pipozoft/astrobot/eyes/heart_eye/astrobot11.png

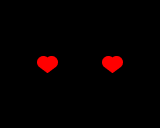
eyes/heart_eye/astrobot11.png
