pipozoft/astrobot/eyes/heart_eye/astrobot18.png

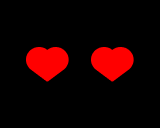
eyes/heart_eye/astrobot18.png
