pipozoft/astrobot/eyes/heart_eye/astrobot23.png

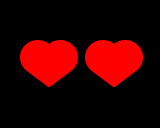
eyes/heart_eye/astrobot23.png
