pipozoft/astrobot/Micro5_Clock.h

#pragma once
#include <Adafruit_GFX.h>

const uint8_t Micro5_ClockBitmaps[] PROGMEM = {
  0x00, 0xFF, 0xFF, 0xFF, 0xFF, 0xFF, 0xFF, 0xFF, 0xFF, 0xFF, 0xFF, 0xFF, 0xFF, 0xFF, 0xFF, 0xFF,
  0xFF, 0xFF, 0xFF, 0xFF, 0xFF, 0xFF, 0xFF, 0xFF, 0xFF, 0xFF, 0xFF, 0xFF, 0xFF, 0xFF, 0xFF, 0xE0,
  0x1F, 0xFF, 0xF8, 0x07, 0xFF, 0xFE, 0x01, 0xFF, 0xFF, 0x80, 0x7F, 0xFF, 0xE0, 0x1F, 0xFF, 0xF8,
  0x07, 0xFF, 0xFE, 0x01, 0xFF, 0xFF, 0x80, 0x7F, 0xFF, 0xE0, 0x1F, 0xFF, 0xF8, 0x07, 0xFF, 0xFE,
  0x01, 0xFF, 0xFF, 0x80, 0x7F, 0xFF, 0xE0, 0x1F, 0xFF, 0xF8, 0x07, 0xFF, 0xFE, 0x01, 0xFF, 0xFF,
  0x80, 0x7F, 0xFF, 0xE0, 0x1F, 0xFF, 0xF8, 0x07, 0xFF, 0xFE, 0x01, 0xFF, 0xFF, 0x80, 0x7F, 0xFF,
  0xE0, 0x1F, 0xFF, 0xF8, 0x07, 0xFF, 0xFE, 0x01, 0xFF, 0xFF, 0x80, 0x7F, 0xFF, 0xE0, 0x1F, 0xFF,
  0xFF, 0xFF, 0xFF, 0xFF, 0xFF, 0xFF, 0xFF, 0xFF, 0xFF, 0xFF, 0xFF, 0xFF, 0xFF, 0xFF, 0xFF, 0xFF,
  0xFF, 0xFF, 0xFF, 0xFF, 0xFF, 0xFF, 0xFF, 0xFF, 0xFF, 0xFF, 0xFF, 0xFF, 0xFC, 0xFF, 0xFF, 0xFF,
  0xFF, 0xFF, 0xFF, 0xFF, 0xFF, 0xFF, 0xFF, 0xFF, 0xFF, 0xFF, 0xFF, 0xFF, 0xFF, 0xFF, 0xFF, 0xFF,
  0x80, 0x3F, 0xC0, 0x1F, 0xE0, 0x0F, 0xF0, 0x07, 0xF8, 0x03, 0xFC, 0x01, 0xFE, 0xFF, 0xFF, 0xFF,
  0xFF, 0xFF, 0xFF, 0xFF, 0xFF, 0xFF, 0xFF, 0xFF, 0xFF, 0xFF, 0xFF, 0xFF, 0xFF, 0xFF, 0xFF, 0xFF,
  0x80, 0x3F, 0xC0, 0x1F, 0xE0, 0x0F, 0xF0, 0x07, 0xF8, 0x03, 0xFC, 0x01, 0xFE, 0x00, 0xFF, 0x00,
  0x7F, 0x80, 0x3F, 0xC0, 0x1F, 0xE0, 0x0F, 0xF0, 0x07, 0xF8, 0x03, 0xFC, 0x01, 0xFE, 0x00, 0xFF,
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
  {0, 0, 0, 0, 0, 0},  // 0x44 'D'
  {0, 0, 0, 0, 0, 0},  // 0x45 'E'
  {0, 0, 0, 0, 0, 0},  // 0x46 'F'
  {0, 0, 0, 0, 0, 0},  // 0x47 'G'
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
};

const GFXfont Micro5_Clock PROGMEM = {
  (uint8_t *)Micro5_ClockBitmaps,
  (GFXglyph *)Micro5_ClockGlyphs,
  0x20, 0x50, 94
};
