pipozoft/astrobot/pixel_data.h

// astrobot1.png
const unsigned char white_pixels_astrobot1[][2] PROGMEM = {{56,51}, {29,76}, {43,59}, {47,64}, {21,68}, {19,60}, {25,67}, {25,45}, {41,62}, {44,64}, {52,59}, {51,75}, {42,43}, {48,74}, {49,78}, {40,47}, {41,44}, {38,68}, {55,46}, {43,51}, {36,75}, {30,71}, {39,46}, {55,49}, {23,55}, {49,73}, {32,56}, {50,42}, {34,49}, {34,68}, {34,74}, {46,40}, {53,52}, {44,63}, {51,50}, {29,71}, {55,67}, {35,70}, {40,69}, {36,58}, {31,67}, {32,49}, {60,64}, {42,62}, {42,77}, {24,48}, {42,79}, {43,68}, {47,53}, {55,51}, {57,67}, {28,75}, {22,48}, {44,48}, {43,49}, {46,53}, {36,76}, {40,56}, {21,65}, {42,61}, {25,57}, {45,60}, {39,49}, {49,66}, {48,79}, {42,50}, {52,75}, {38,61}, {41,46}, {28,49}, {50,60}, {48,61}, {32,50}, {31,74}, {31,49}, {22,49}, {31,50}, {31,52}, {31,53}, {58,51}, {23,64}, {28,68}, {47,58}, {47,59}, {33,74}, {37,62}, {43,47}, {30,62}, {50,44}, {32,51}, {43,42}, {26,53}, {38,56}, {36,65}, {19,62}, {33,53}, {25,51}, {50,57}, {48,42}, {44,78}, {58,55}, {48,78}, {37,39}, {50,71}, {24,45}, {32,75}, {51,53}, {40,66}, {45,42}, {48,54}, {18,58}, {53,71}, {40,78}, {28,50}, {54,65}, {45,78}, {30,73}, {20,53}, {34,65}, {38,49}, {18,57}, {43,40}, {47,52}, {56,47}, {25,55}, {37,54}, {59,58}, {38,67}, {34,70}, {36,52}, {42,54}, {35,39}, {40,46}, {40,64}, {53,67}, {46,62}, {27,77}, {33,75}, {27,66}, {38,71}, {52,45}, {35,68}, {48,59}, {42,75}, {24,56}, {38,62}, {29,43}, {58,66}, {21,60}, {39,64}, {52,57}, {44,74}, {40,70}, {42,63}, {19,54}, {33,48}, {52,54}, {31,71}, {27,70}, {42,59}, {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
