pipozoft/astrobot/Micro5_Regular48pt7b.h

const uint8_t Micro5_Regular48pt7bBitmaps[] PROGMEM = {
  0x00, 0xFF, 0xFF, 0xFF, 0xFF, 0xFF, 0xFF, 0xFF, 0xFF, 0xFF, 0xFF, 0xFF,
  0xFF, 0xFF, 0xFF, 0xFF, 0xFF, 0xFF, 0xFF, 0xFF, 0xFF, 0xFF, 0xFF, 0xFF,
  0xFF, 0xFF, 0xFF, 0xFF, 0xFF, 0xFF, 0xC0, 0x00, 0x00, 0x00, 0x00, 0x00,
  0x00, 0x00, 0x00, 0x3F, 0xFF, 0xFF, 0xFF, 0xFF, 0xFF, 0xFF, 0xFF, 0xFF,
  0xFF, 0xE0, 0xFF, 0x80, 0x7F, 0xFF, 0xE0, 0x1F, 0xFF, 0xF8, 0x07, 0xFF,
  0xFE, 0x01, 0xFF, 0xFF, 0x80, 0x7F, 0xFF, 0xE0, 0x1F, 0xFF, 0xF8, 0x07,
  0xFF, 0xFE, 0x01, 0xFF, 0xFF, 0x80, 0x7F, 0xFF, 0xE0, 0x1F, 0xFF, 0xF8,
  0x07, 0xFF, 0xFE, 0x01, 0xFF, 0xFF, 0x80, 0x7F, 0xFF, 0xE0, 0x1F, 0xFF,
  0xF8, 0x07, 0xFF, 0xFE, 0x01, 0xFF, 0xFF, 0x80, 0x7F, 0xC0, 0x00, 0x00,
  0x7F, 0xC0, 0x3F, 0xE0, 0x00, 0x0F, 0xF8, 0x07, 0xFC, 0x00, 0x01, 0xFF,
  0x00, 0xFF, 0x80, 0x00, 0x3F, 0xE0, 0x1F, 0xF0, 0x00, 0x07, 0xFC, 0x03,
  0xFE, 0x00, 0x00, 0xFF, 0x80, 0x7F, 0xC0, 0x00, 0x1F, 0xF0, 0x0F, 0xF8,
  0x00, 0x03, 0xFE, 0x01, 0xFF, 0x00, 0x00, 0x7F, 0xC0, 0x3F, 0xFF, 0xFF,
  0xFF, 0xFF, 0xFF, 0xFF, 0xFF, 0xFF, 0xFF, 0xFF, 0xFF, 0xFF, 0xFF, 0xFF,
  0xFF, 0xFF, 0xFF, 0xFF, 0xFF, 0xFF, 0xFF, 0xFF, 0xFF, 0xFF, 0xFF, 0xFF,
  0xFF, 0xFF, 0xFF, 0xFF, 0xFF, 0xFF, 0xFF, 0xFF, 0xFF, 0xFF, 0xFF, 0xFF,
  0xFF, 0xFF, 0xFF, 0xFF, 0xFF, 0xE0, 0x0F, 0xF0, 0x07, 0xF8, 0x00, 0x01,
  0xFE, 0x00, 0xFF, 0x00, 0x00, 0x3F, 0xC0, 0x1F, 0xE0, 0x00, 0x07, 0xF8,
  0x03, 0xFC, 0x00, 0x00, 0xFF, 0x00, 0x7F, 0x80, 0x00, 0x1F, 0xE0, 0x0F,
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
  {  4660,  26,  43,  34,    0,  -42 },   // 0x46 'F'
  {  4800,  26,  43,  34,    0,  -42 },   // 0x47 'G'
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

const GFXfont Micro5_Regular48pt7b PROGMEM = {
  (uint8_t  *)Micro5_Regular48pt7bBitmaps,
  (GFXglyph *)Micro5_Regular48pt7bGlyphs,
  0x20, 0x7E, 94 };

// Approx. 12422 bytes
