pipozoft/astrobot/notes.h

#define Ab3 233
#define C4 262
#define Ab2 117
#define D5 587
#define F2 87
#define C5 523
#define G2 98
#define Db2 78
#define Ab4 466

const int midi1[][3] = {
 {Ab3, 462, 0},
 {C4, 462, 0},
 {Ab2, 115, 0},
 {Ab2, 115, 115},
 {Ab2, 115, 0},
 {D5, 231, 0},
 {F2, 115, 115},
 {F2, 115, 231},
 {F2, 115, 115},
 {F2, 115, 0},
 {D5, 231, 0},
 {C5, 231, 0},
 {G2, 115, 231},
 {G2, 115, 231},
 {G2, 115, 0},
 {D5, 231, 0},
 {Db2, 115, 115},
 {Db2, 115, 231},
 {Ab4, 231, 0},
};
// Generated using https://github.com/ShivamJoker/MIDI-to-Arduino
